URJCMakerGroup/TFG-Cristina-Fernandez/Images/Big/Esquema_funcionamiento_mesa_modelado.png

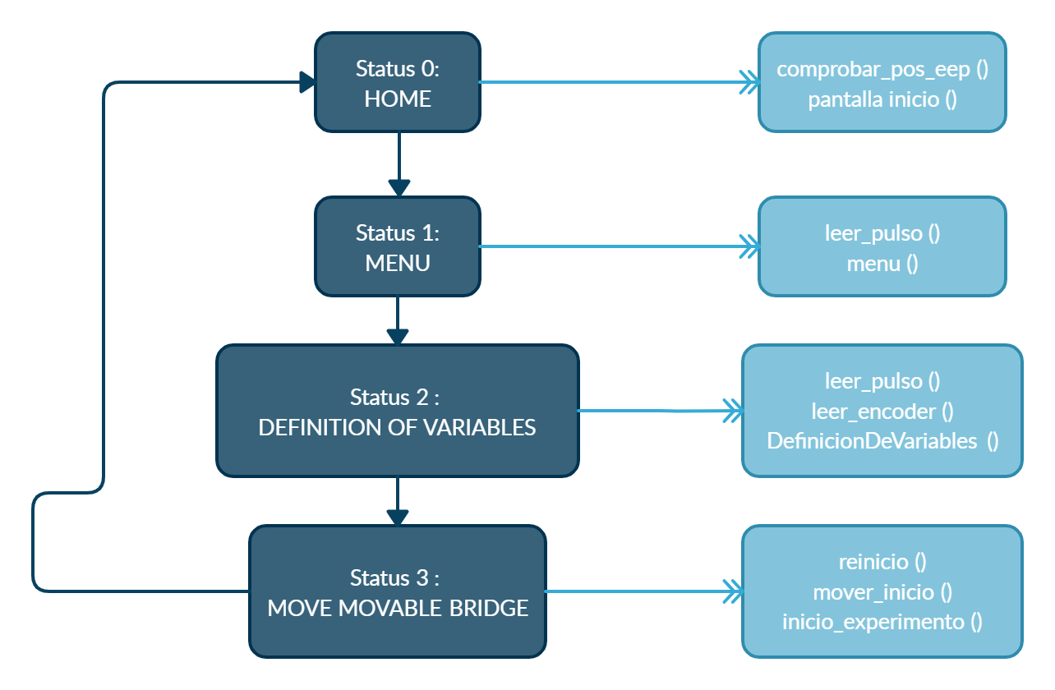
Images/Big/Esquema_funcionamiento_mesa_modelado.png
