URJCMakerGroup/TFG-Cristina-Fernandez/Images/Big/EtapaB.PNG

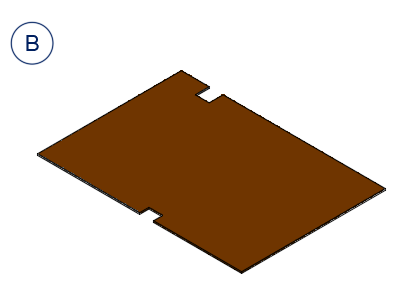
Images/Big/EtapaB.PNG
