URJCMakerGroup/TFG-Cristina-Fernandez/Images/Big/EtapaC.PNG

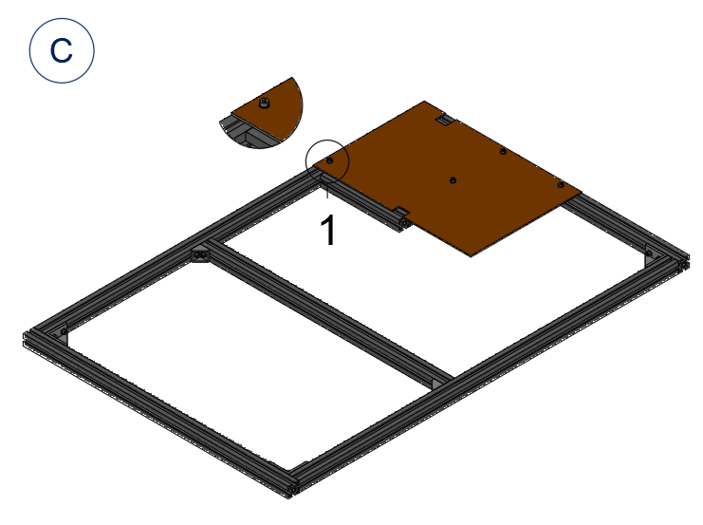
Images/Big/EtapaC.PNG
