URJCMakerGroup/TFG-Cristina-Fernandez/Images/Big/EtapaD.PNG

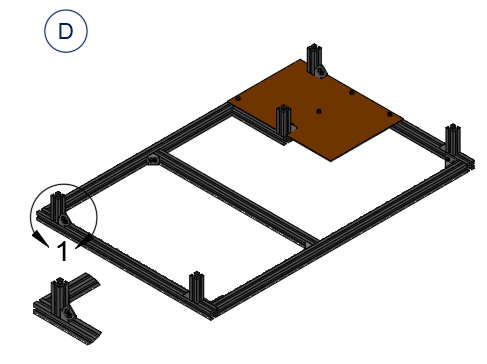
Images/Big/EtapaD.PNG
