URJCMakerGroup/TFG-Cristina-Fernandez/Images/Big/EtapaE.PNG

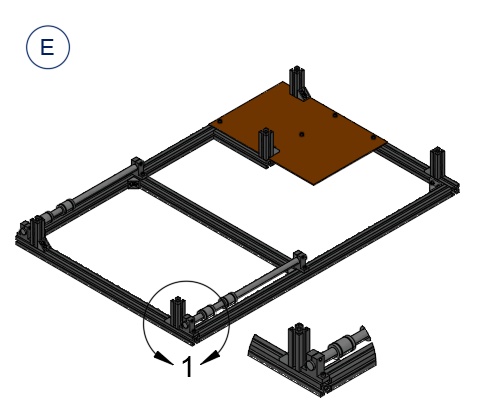
Images/Big/EtapaE.PNG
