URJCMakerGroup/TFG-Cristina-Fernandez/Images/Big/EtapaF.PNG

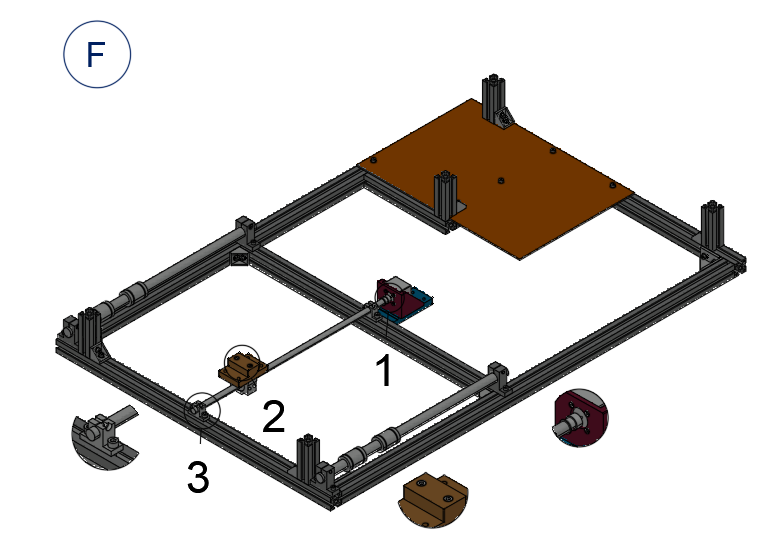
Images/Big/EtapaF.PNG
