URJCMakerGroup/TFG-Cristina-Fernandez/Images/Big/EtapaG.PNG

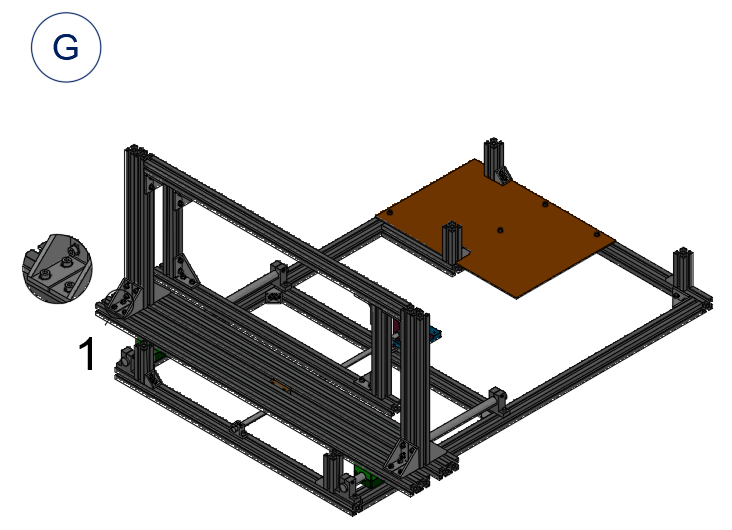
Images/Big/EtapaG.PNG
