URJCMakerGroup/TFG-Cristina-Fernandez/Images/Big/EtapaH.PNG

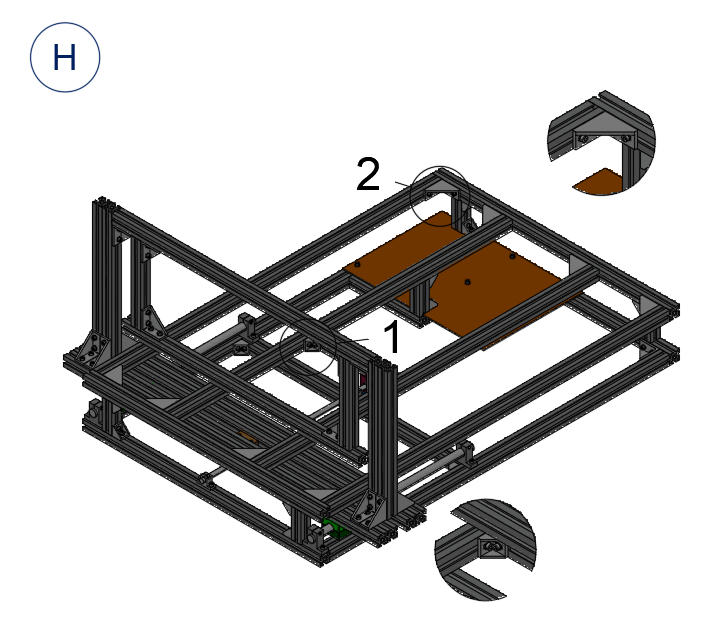
Images/Big/EtapaH.PNG
