URJCMakerGroup/TFG-Cristina-Fernandez/Images/Big/EtapaI.PNG

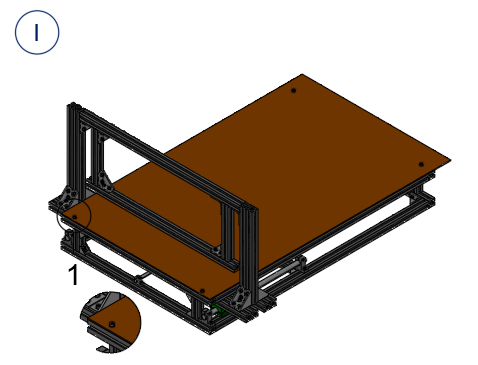
Images/Big/EtapaI.PNG
