URJCMakerGroup/TFG-Cristina-Fernandez/Images/Big/Mesa_modelado.png

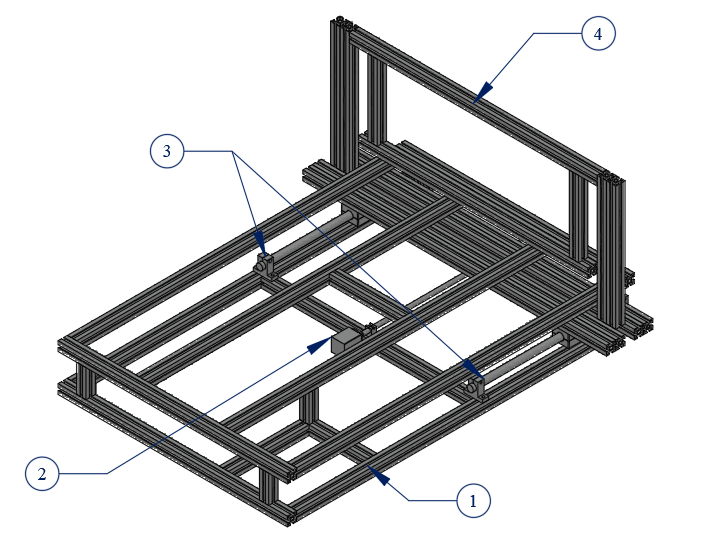
Images/Big/Mesa_modelado.png
