URJCMakerGroup/TFG-Cristina-Fernandez/Images/Big/OSHW_mark_ES000021.png

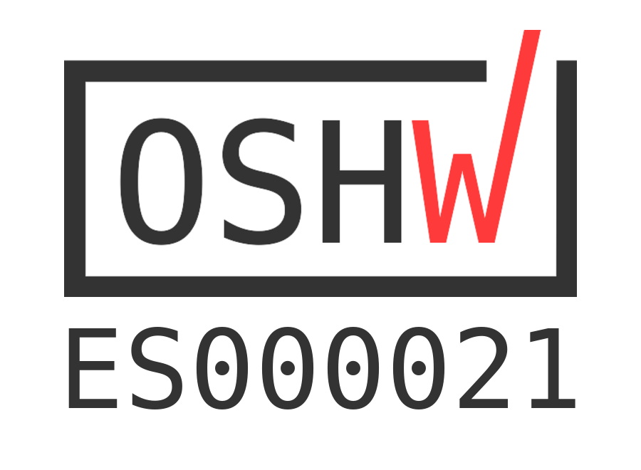
Images/Big/OSHW_mark_ES000021.png
