URJCMakerGroup/TFG-Cristina-Fernandez/Images/Big/Pantalla_LCD.PNG

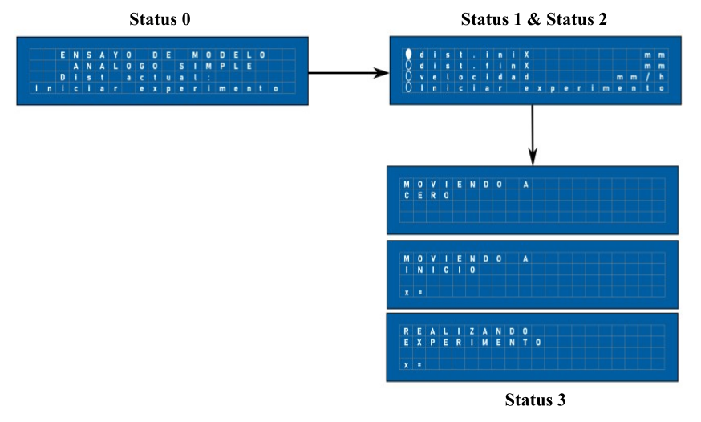
Images/Big/Pantalla_LCD.PNG
