URJCMakerGroup/TFG-Cristina-Fernandez/Images/Big/Simulador.PNG

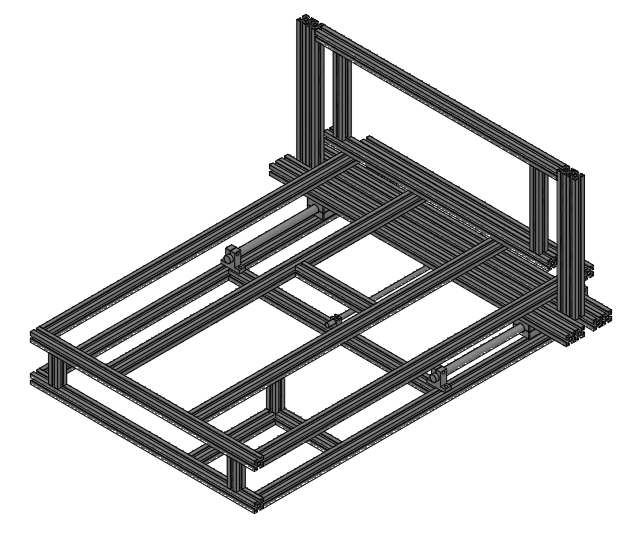
Images/Big/Simulador.PNG
