URJCMakerGroup/TFG-Cristina-Fernandez/Images/Big/Simulador_tablas.PNG

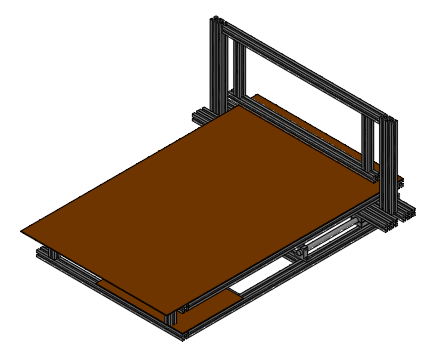
Images/Big/Simulador_tablas.PNG
