URJCMakerGroup/TFG-Cristina-Fernandez/img/Big/Soporte_Cojinete_superior.PNG

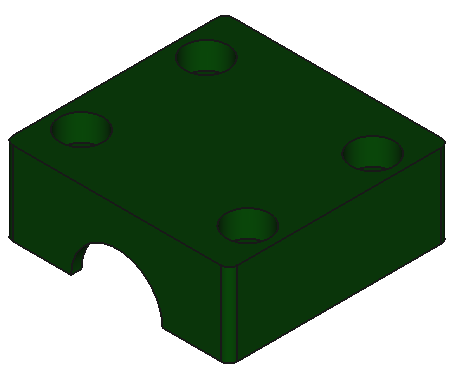
img/Big/Soporte_Cojinete_superior.PNG
