URJCMakerGroup/TFG-Cristina-Fernandez/src/geo_mesa.py

# ----------------------------------------------------------------------------
# -- Simulador geologico
# ----------------------------------------------------------------------------
# -- (c) Felipe Machado
# -- Area of Electronic Technology. Rey Juan Carlos University (urjc.es)
# -- July-2019
# ----------------------------------------------------------------------------
# --- LGPL Licence
# ----------------------------------------------------------------------------

# to execute from the FreeCAD console:
#  execute freecad from the cmd console on the directory
# "C:\Program Files\FreeCAD 0.16\bin\freecad" base.py

# to excute from command line in windows:
# "C:\Program Files\FreeCAD 0.16\bin\freecadcmd" base.py

# with FreeCAD 0.18 Python 3
#exec(open("geo_mesa.py").read())

import os
import sys
import math
import FreeCAD
import FreeCADGui
import Part
import Draft
import logging  # to avoid using print statements
import time
#import copy
#import Mesh
import DraftVecUtils


# to get the current directory. Freecad has to be executed from the same
# directory this file is
filepath = os.getcwd()
#filepath = "./"
#filepath = "F/urjc/proyectos/2016_platform_cell/device/planos/python/"
#filepath = "C:/Users/felipe/urjc/proyectos/2016_platform_cell/device/planos/python/"


# to get the components
# In FreeCAD can be added: Preferences->General->Macro->Macro path
sys.path.append(filepath) 
# Either one of these 2 to select the path, inside the tree, copied by
# git subtree, or in its one place
#sys.path.append(filepath + '/' + 'modules/comps')
sys.path.append(filepath + '/' + '../../comps')

import fcfun   # import my functions for freecad. FreeCad Functions
import kcomp   # import material constants and other constants
import comps   # import my CAD components
import parts   # import my CAD components to print

from fcfun import V0, VX, VY, VZ, V0ROT, addBox, addCyl, fillet_len
from fcfun import VXN, VYN, VZN
from fcfun import addBolt, addBoltNut_hole, NutHole
from kcomp import TOL

def str_neg (num, p=0, n=0):
    """ Just a function to have the names of componentes when using for
    to differenciate them if the index is negative. FreeCAD name cannot
    have negative, so writting a 'n' instead of a '-'
    
    Parameters:
    ----------
    num : int
        the number (index of a for loop)
    p : int
        0: doesnt write a p when number is positive
        1: writes a p when number is positive
    n : int
        0: doesnt write the number, just the n or p (if p=1)
        1: writes the number, and the n if the case (or p)
    """

    if num < 0:
       if n == 0: # dont write the number
           return 'n'
       else: # write the number
           return 'n' + str(abs(num))
    else: # positive
       if n == 0: # dont write the number
           if p == 0:
               return ''
           else: # write the p, not the number
               return 'p'
       else: # write the number
           if p == 0:
               return str(num)
           else: # write the p and the number
               return 'p' + str(num)



# Taking the same axis as the 3D printer:
#
#    Z   Y
#    | /               USING THIS ONE
#    |/___ X
# 
# centered on the cubes and the vertical line of the camera and the objective
#
# as seen from the front
# be careful because at the beginning I was considering:
#      Z
#      |
#      |___ Y       NOT USING THIS ONE
#     /
#    / X
#
# In this design, the bas will be centered on X

logging.basicConfig(level=logging.DEBUG,
                    format='%(asctime)s - %(levelname)s - %(message)s')

doc = FreeCAD.newDocument()

#Gui.ActiveDocument = Gui.getDocument(doc.Label)
#guidoc = Gui.getDocument(doc.Label)


# file to save the components and their dimensions. Kind of a BOM,
# bill of materials
file_comps = open ('geo_bom.txt', 'w')

tot_d = 1000 #largo (profundidad interna)
tot_w = 740 #ancho
alu_w = 30 # ancho de los perfiles

alu_len_d = tot_d + 2 * alu_w  #perfiles a lo largo (profundo)
alu_len_v = 90  #perfiles a lo alto para mesa REVISAR
alu_len_w = tot_w #perfiles a lo ancho
alu_len_w_int1 = tot_w - 2 * alu_w #perfil a lo ancho interior de la base de la estructura
alu_len_w_int2 = tot_w #perfiles a lo ancho interiores del puente móvil

# portico horizontal parte arriba
alu_len_gantry = tot_w + 60. # poner un extra para que no rocen (mirar)

# carriage width (length=
#2: each side. 3: to have a double profile and a double bracket
alu_car_l = tot_w + 2 * 3 * alu_w + 60. #(mirar)

carro_color = fcfun.ORANGE_08
empuje_color = fcfun.GREEN_07
w_color = fcfun.BLUE_07

d_alu = kcomp.ALU_PROF[alu_w]

# zero in the Y of motor leadscrew support, centered on Y
# Z on top of the aluminum profiles
pos_0_x = 0.
pos_0_y = 0.
pos_0_z = 0.

# todas las posiciones como si pos_0 estuviese en (0,0,0)
pos_0 = FreeCAD.Vector(pos_0_x, pos_0_y, pos_0_z)

rod_d = 20. #diameter of the rods

leadscrew_tot_l = 510. #(mirar)
leadscrew_motor_space_l = 30.
leadscrew_int_l = leadscrew_tot_l - leadscrew_motor_space_l
leadscrew_d = 12 # trapecial, or 16.

# perfiles del portico en altura
alu_len_port_v = 400

# perfiles que bajan del portico para empujar
alu_len_empuje_v = 244

alu_tray_name = 'alu_tray'

# travesano interno para el final del husillo y su soporte
alu_base_traves_int_pos = DraftVecUtils.scale(VY, leadscrew_int_l-alu_w/2)
h_alu = comps.getaluprof_dir(d_alu, length=alu_len_w_int1,
                                 fc_axis_l = VX,
                                 fc_axis_w = VY,
                                 fc_axis_p = VZN,
                                 ref_l = 1, # centered
                                 ref_w = 1, # centered
                                 ref_p = 2, # at top
                                 wfco = 1,
                                 pos = alu_base_traves_int_pos + pos_0,
                                 name = 'travesano_int')

print ('travesanos ancho: ', str(alu_len_w))
# los travesanos en direccion x, cubren el ancho
for y_i in [0,1]:  # 
    alu_name = 'alu_travesano_base' + '_y' + str(y_i)
    alu_base_traves_pos = DraftVecUtils.scale(VY, y_i*(alu_len_d+alu_w))
    h_alu = comps.getaluprof_dir(d_alu, length=alu_len_w,
                                 fc_axis_l = VX,
                                 fc_axis_w = VY,
                                 fc_axis_p = VZN,
                                 ref_l = 1, # centered
                                 ref_w = 1, # centered
                                 ref_p = 2, # at top
                                 wfco = 1,
                                 pos = alu_base_traves_pos + pos_0,
                                 name = alu_name)

# soportes de ejes
for x_i in [-1,1]:  # izquierda y derecha
    sh_pos1 = alu_base_traves_int_pos + DraftVecUtils.scale(VX, x_i*tot_w/2) 
    sh_name1 = 'sh_' + '_y' + str(1) + '_x' + str_neg(x_i)
    h_sh8_1 = comps.Sk_dir(size=rod_d,
                         fc_axis_h = VZ,
                         fc_axis_d = VY,
                         fc_axis_w = DraftVecUtils.scale(VXN,x_i),
                         ref_hr = 0,
                         ref_wc = -1, #at the end
                         ref_dc = 1,
                         tol=0, # not to print
                         pos=sh_pos1 + pos_0,
                         name = sh_name1)
    
    sh_pos2 = DraftVecUtils.scale(VX, x_i*tot_w/2) 
    sh_name2 = 'sh_' + '_y' + str(2) + '_x' + str_neg(x_i)
    h_sh8_2 = comps.Sk_dir(size=rod_d,
                         fc_axis_h = VZ,
                         fc_axis_d = VY,
                         fc_axis_w = DraftVecUtils.scale(VXN,x_i),
                         ref_hr = 0,
                         ref_wc = -1, #at the end
                         ref_dc = 1,
                         tol=0, # not to print
                         pos=sh_pos2 + pos_0,
                         name = sh_name2)
    

file_comps.write('perfiles de la base y mesa 30x30, travesanos: \n')
file_comps.write('4 x ' + str(alu_len_w) + ' \n')
file_comps.write('      perfil interno soporte husillo (alguno mas) \n')
file_comps.write('4 x ' + str(alu_len_w_int1) + ' \n')

# height of the axis, from pos_0
axis_h = h_sh8_1.axis_h

# distance from the side to the center of the SH
axis_cen_w = h_sh8_1.tot_w/2

axis_len = alu_len_d/2. - alu_w


#dictionary of the linear bearing housing
d_linbear_house = kcomp.SCE20UU_Pr30b

# separacion de los postes verticales del portico de la mesa, a cada lado
port_sep = 30.

print ('largeros: largo: ', str(alu_len_d))
# los largueros en direccion y, cubren la profundidad (depth)
for x_i in [-1,1]:  # izquierda y derecha
    alu_name = 'alu_largo_base' + '_x' + str_neg(x_i)
    alu_base_largo_pos = (DraftVecUtils.scale(VX, x_i*tot_w/2) 
                             + DraftVecUtils.scale(VY, alu_w/2) )

    h_alu = comps.getaluprof_dir(d_alu, length=alu_len_d,
                                 fc_axis_l = VY,
                                 fc_axis_w = DraftVecUtils.scale(VXN,x_i),
                                 fc_axis_p = VZN,
                                 ref_l = 2, # from the side
                                 ref_w = 2, # from the side
                                 ref_p = 2, # at top
                                 wfco = 1,
                                 pos = alu_base_largo_pos + pos_0,
                                 name = alu_name)

    # ejes
    axis_pos = (DraftVecUtils.scale(VX, x_i*(tot_w/2-axis_cen_w)) 
                      + DraftVecUtils.scale(VY, -alu_w/2)
                      + DraftVecUtils.scale(VZ, axis_h)  )
    
    shp_rod = fcfun.shp_cyl_gen(r = rod_d/2., h=axis_len,
                              axis_h = VY,
                              pos_h = 1,
                              pos = axis_pos + pos_0)
    Part.show(shp_rod)

    for y_i in [0,1]:  # 
        # Para uno de 4, todos en una pieza
        linbear_pos_y = DraftVecUtils.scale(VY,3*alu_w + y_i*alu_w)
        linbear1_pos_y = DraftVecUtils.scale(VY,3*alu_w)
        linbear_pos_y = DraftVecUtils.scale(VY,3*alu_w + y_i*3*alu_w)
        linbear_pos  = axis_pos + linbear_pos_y
        h_linbear_house = parts.LinBearHouse(d_linbear_house,
                                             fc_slide_axis = VY,
                                             fc_bot_axis=VZ,
                                             axis_center = 1,
                                             mid_center = 1,
                                             pos = linbear_pos + pos_0)
        # height of the base of the aluminum profile of carriage, from pos_0

        alu_carr_trav_h = kcomp.SCE20UU_Pr30b['axis_h']

        # perfiles del carro
        if x_i == 1: # estan centrados en x
            alu_car_name = 'alu_car'
            for it_y in [-1,0]: # a double profile
                alu_car_pos  = (DraftVecUtils.scale(VZ, axis_h)
                + DraftVecUtils.scale(VZ, alu_carr_trav_h)
                + linbear_pos_y +
                + DraftVecUtils.scale(VY,it_y*d_linbear_house['bolt_sep_l']))
               
                h_alu = comps.getaluprof_dir(d_alu, length=alu_car_l,
                                             fc_axis_l = VX,
                                             fc_axis_w = VY,
                                             fc_axis_p = VZ,
                                             ref_l = 1, # centered
                                             ref_w = 1, # centered
                                             ref_p = 2, # at bottom
                                             wfco = 1,
                                             pos = alu_car_pos + pos_0,
                                             name = alu_car_name)
                #h_alu.color(carro_color)

    #perfiles verticales del portico, no se si dobles a simples
    # solo hay uno por cada lado
    port_pos_y = linbear1_pos_y + DraftVecUtils.scale(VY, alu_w)
    port_pos_z = DraftVecUtils.scale(VZ, axis_h + alu_carr_trav_h + alu_w)
    for it_x in[0,1]: # a double profile
        alu_port_name = 'alu_port_v' + str_neg(x_i,p=1, n=0)
        alu_port_v_pos  = (port_pos_y + port_pos_z
           + DraftVecUtils.scale(VX,x_i*(port_sep + alu_len_w/2. +it_x*alu_w)))
               
        h_alu = comps.getaluprof_dir(d_alu, length=alu_len_port_v,
                                      fc_axis_l = VZ,
                                      fc_axis_w = DraftVecUtils.scale(VX,x_i),
                                      fc_axis_p = VY,
                                      ref_l = 2, # at bottom
                                      ref_w = 2, # at the end
                                      ref_p = 1, # centered
                                      wfco = 1,
                                      pos = alu_port_v_pos + pos_0,
                                      name = alu_port_name)
        #h_alu.color(carro_color)

topgantry_pos_z = port_pos_z + DraftVecUtils.scale(VZ, alu_len_port_v)
topgantry_pos = port_pos_y + topgantry_pos_z
h_alu_topgantry = comps.getaluprof_dir(d_alu, length=alu_len_gantry,
                                      fc_axis_l = VX,
                                      fc_axis_w = VY,
                                      fc_axis_p = VZN,
                                      ref_l = 1, # centered bottom
                                      ref_w = 1, # centered
                                      ref_p = 2, # at top
                                      wfco = 1,
                                      pos = topgantry_pos + pos_0,
                                      name = 'top_gantry')

#h_alu_topgantry.color(carro_color)

empuje_v_pos_z = topgantry_pos_z + DraftVecUtils.scale(VZN, alu_w)

# perfiles que bajan del portico para empujar
for x_i in [-1,1]:  # izquierda y derecha
    alu_name = 'alu_empuje_v' + '_x' + str_neg(x_i, p=1)
    empuje_v_pos_x = DraftVecUtils.scale(VX, x_i * (alu_len_w_int2/2. - 30.))
    empuje_v_pos = empuje_v_pos_x + port_pos_y + empuje_v_pos_z 
    h_alu_empuje_v = comps.getaluprof_dir(d_alu, length=alu_len_empuje_v,
                                      fc_axis_l = VZN,
                                      fc_axis_w = DraftVecUtils.scale(VXN,x_i),
                                      fc_axis_p = VY,
                                      ref_l = 2, # from top
                                      ref_w = 2, # from outer side
                                      ref_p = 1, # centered
                                      wfco = 1,
                                      pos = empuje_v_pos + pos_0,
                                      name = alu_port_name)
    #h_alu_empuje_v.color(empuje_color)

file_comps.write('perfiles que bajan del portico para empujar\n')
file_comps.write('4 x ' + str(alu_len_empuje_v) + '\n')

file_comps.write('perfiles que bajan del portico para empujar (otra altura)\n')
file_comps.write('4 x ' + str(alu_len_empuje_v-50) + '\n')

file_comps.write('\n2 Ejes: \n')
file_comps.write('largo:' + str(axis_len) + '  diametro :' + str(rod_d) + '\n\n')

# perfil de la base del empuje
base_empuje_pos_z = empuje_v_pos_z + DraftVecUtils.scale(VZN, alu_len_empuje_v)
base_empuje_pos = port_pos_y + base_empuje_pos_z 
h_alu_base_empuje = comps.getaluprof_dir(d_alu, length=alu_len_w_int2,
                                      fc_axis_l = VX,
                                      fc_axis_w = VY,
                                      fc_axis_p = VZN,
                                      ref_l = 1, # from top
                                      ref_w = 1, # from outer side
                                      ref_p = 2, # from top
                                      wfco = 1,
                                      pos = base_empuje_pos + pos_0,
                                      name = 'alu_base_empuje')
#h_alu_base_empuje.color(empuje_color)

file_comps.write('largueros de la base y mesa, dos más a lo largo \n')
file_comps.write('6 x ' + str(alu_len_d) + '\n')
file_comps.write('perfiles del carro 2x30x30 (dobles) \n')
file_comps.write('2 x ' + str(alu_car_l) + '\n')

file_comps.write('perfil de la base del empuje\n')
file_comps.write( str(alu_len_w_int2) + '\n')

file_comps.write('perfil de la base del empuje: extras (-60)\n')
file_comps.write( str(alu_len_w_int2-60) + '\n')

file_comps.write('perfil de la base del empuje: extras (-120)\n')
file_comps.write( str(alu_len_w_int2-120) + '\n')

min_mesa_h = axis_h + alu_carr_trav_h + alu_w
print('altura entre perfil de la base (top) y perfil del carro (top): ')
print(str(min_mesa_h), '\n')
            
# para tenerlo en la siguiente decena más alta, y con minimo 2 mm
mesa_h = 10* math.ceil((min_mesa_h +2) / 10.)
if (mesa_h - min_mesa_h) > 15:
    mesa_h = mesa_h - 10
print (str(mesa_h))

file_comps.write('perfiles del portico 2x30x30 (dobles) \n')
file_comps.write('2 x ' + str(alu_len_port_v) + '\n')
file_comps.write('también pueden ser simples 30x30 \n')
file_comps.write('2 x ' + str(alu_len_port_v) + '\n')
file_comps.write('puente del portico \n')
file_comps.write('1 x ' + str(alu_len_gantry) + '\n')

file_comps.write('altura entre perfil de la base (top) y perfil de carro (top): ')
file_comps.write(str(min_mesa_h) + '\n')

file_comps.write('perfiles elevacion mesa 30x30 \n')
file_comps.write('10 x ' + str(mesa_h) + '\n')

for x_i in [-1,1]:  # izquierda y derecha
   for y_i in [0,1]:  #delante y detras
       pos_alu_v = (pos_0 + DraftVecUtils.scale(VY, y_i*(alu_len_d+alu_w))
                         + DraftVecUtils.scale(VX, x_i*(tot_w/2-2*axis_cen_w))) 
       h_alu_v = comps.getaluprof_dir(d_alu, length=mesa_h,
                                   fc_axis_l = VZ,
                                   fc_axis_w = DraftVecUtils.scale(VXN,x_i),
                                   fc_axis_p = VY,
                                   ref_l = 2, # at bottom
                                   ref_w = 2, # at the end
                                   ref_p = 1, # centered
                                   wfco = 1,
                                   pos = pos_alu_v,
                                   name = 'alu_v')

#Perfiles de la mesa, ya contabilizados arriba, porque son las mismas
# dimensiones que la base
for y_i in [0,1]:  # 
    alu_name = 'alu_travesano_mesa' + '_y' + str(y_i)
    alu_base_traves_pos = (pos_0
                           + DraftVecUtils.scale(VY, y_i*(alu_len_d+alu_w))
                           + DraftVecUtils.scale(VZ,mesa_h))
    h_alu = comps.getaluprof_dir(d_alu, length=alu_len_w,
                                 fc_axis_l = VX,
                                 fc_axis_w = VY,
                                 fc_axis_p = VZ,
                                 ref_l = 1, # centered
                                 ref_w = 1, # centered
                                 ref_p = 2, # at top
                                 wfco = 1,
                                 pos = alu_base_traves_pos,
                                 name = alu_name)

for x_i in [-1,1]:  # izquierda y derecha
    alu_name = 'alu_largo_mesa' + '_x' + str_neg(x_i)
    alu_mesa_largo_pos = (pos_0 + DraftVecUtils.scale(VX, x_i*tot_w/2) 
                             + DraftVecUtils.scale(VY, alu_w/2) 
                           + DraftVecUtils.scale(VZ,mesa_h))

    h_alu = comps.getaluprof_dir(d_alu, length=alu_len_d,
                                 fc_axis_l = VY,
                                 fc_axis_w = DraftVecUtils.scale(VXN,x_i),
                                 fc_axis_p = VZ,
                                 ref_l = 2, # from the side
                                 ref_w = 2, # from the side
                                 ref_p = 2, # at top
                                 wfco = 1,
                                 pos = alu_mesa_largo_pos,
                                 name = alu_name)

# Pillow block soporte de husillo (dibujo aproximado)
for y_i in [0,1]:  # delante detras
    pillow_pos = DraftVecUtils.scale(VY, y_i*(leadscrew_int_l-alu_w/2)) 
    pillow_name = 'pillow_' + '_y' + str(y_i) 
    h_pillow = comps.Sk_dir(size=leadscrew_d,
                             fc_axis_h = VZ,
                             fc_axis_d = VY,
                             fc_axis_w = VX,
                             ref_hr = 0,
                             ref_wc = 1, #centered
                             ref_dc = 1,
                             pillow = 1,
                             tol=0, # not to print
                             pos= pillow_pos + pos_0,
                             name = pillow_name)

# tornillo sin fin
leads_pos = ( DraftVecUtils.scale(VZ, h_pillow.axis_h)
            + DraftVecUtils.scale(VYN, alu_w/2))
shp_leads = fcfun.shp_cyl_gen(r = leadscrew_d/2., h=leadscrew_tot_l,
                              axis_h = VY,
                              pos_h = 1,
                              pos = leads_pos + pos_0)
Part.show(shp_leads)

motor_pos = leads_pos + DraftVecUtils.scale(VY,leadscrew_tot_l)
nema_motor = comps.PartNemaMotor (
                              nema_size = 17,
                              base_l = 56.,
                              shaft_l = 21.,
                              shaft_r = 6.35/2.,
                              circle_r = 47.14/2.,
                              circle_h = 1.6,
                              #chmf_r = chmf_r, 
                              rear_shaft_l= 0,
                              bolt_depth = 5.,
                              #bolt_out  = 0,
                              #cut_extra = 0,
                              axis_d = VZ,
                              axis_w = VX,
                              axis_h = VYN,
                              pos_d = 0,
                              pos_w = 0,
                              pos_h = 2,
                              pos = motor_pos + pos_0)

# los largueros en direccion que sirven de soporte para la tabla
alu_largo_sop = 240
sep_alu_largo = alu_largo_sop + 2 * alu_w

for x_i in [-1,1]:  # izquierda y derecha
    alu_name = 'alu_largo' + '_x' + str_neg(x_i)
    alu_largo_pos = (DraftVecUtils.scale(VX, x_i * sep_alu_largo/2) 
                             + DraftVecUtils.scale(VY, alu_w/2) 
                             + DraftVecUtils.scale(VZ, alu_len_v + alu_w))

    h_alu = comps.getaluprof_dir(d_alu, length=alu_len_d,
                                 fc_axis_l = VY,
                                 fc_axis_w = DraftVecUtils.scale(VXN,x_i),
                                 fc_axis_p = VZN,
                                 ref_l = 2, # from the side
                                 ref_w = 2, # from the side
                                 ref_p = 2, # at top
                                 wfco = 1,
                                 pos = alu_largo_pos + pos_0,
                                 name = alu_name)

# travesano interno superior para el soporte de la tabla
alu_traves_int_sup_pos = (DraftVecUtils.scale(VY, leadscrew_int_l-alu_w/2)
                                 + DraftVecUtils.scale(VZ, alu_len_v + alu_w))

h_alu = comps.getaluprof_dir(d_alu, length=alu_largo_sop,
                                 fc_axis_l = VX,
                                 fc_axis_w = VY,
                                 fc_axis_p = VZN,
                                 ref_l = 1, # centered
                                 ref_w = 1, # centered
                                 ref_p = 2, # at top
                                 wfco = 1,
                                 pos = alu_traves_int_sup_pos + pos_0,
                                 name = 'travesano_int_sup')

# el travesano en direccion x que soporta la tabla con la fuente de alimentación y el Arduino
alu_largo_sop_x = 220
alu_largo_sop_y = 260
alu_traves_sop_x_pos = (DraftVecUtils.scale(VX, (-1)*tot_w/2 + alu_largo_sop_x/2 + alu_w) 
                         + DraftVecUtils.scale(VY, alu_len_d - alu_largo_sop_y))
h_alu = comps.getaluprof_dir(d_alu, length=alu_largo_sop_x,
                             fc_axis_l = VX,
                             fc_axis_w = VY,
                             fc_axis_p = VZN,
                             ref_l = 1, # centered
                             ref_w = 1, # centered
                             ref_p = 2, # at top
                             wfco = 1,
                             pos = alu_traves_sop_x_pos + pos_0,
                             name = 'alu_travesano_sop_x')    

# el travesano en direccion y que soporta la tabla con la fuente de alimentación y el Arduino 
alu_traves_sop_y_pos = (DraftVecUtils.scale(VX, (-1)*tot_w/2 + alu_largo_sop_x + alu_w/2) 
                         + DraftVecUtils.scale(VY, alu_len_d + alu_w/2 - alu_largo_sop_y/2))

h_alu = comps.getaluprof_dir(d_alu, length=alu_largo_sop_y,
                             fc_axis_l = VY,
                             fc_axis_w = VX,
                             fc_axis_p = VZN,
                             ref_l = 1, # centered
                             ref_w = 1, # centered
                             ref_p = 2, # at top
                             wfco = 1,
                             pos = alu_traves_sop_y_pos + pos_0,
                             name = 'alu_travesano_sop_y')    

# el travesano en direccion z 
alu_traves_sop_z_pos = (DraftVecUtils.scale(VX, (-1)*tot_w/2 + alu_largo_sop_x + alu_w) 
                         + DraftVecUtils.scale(VY, alu_len_d - alu_largo_sop_y))

h_alu = comps.getaluprof_dir(d_alu, length=mesa_h,
                             fc_axis_l = VZ,
                             fc_axis_w = VXN,
                             fc_axis_p = VY,
                             ref_l = 2, # centered
                             ref_w = 2, # centered
                             ref_p = 1, # at top
                             wfco = 1,
                             pos = alu_traves_sop_z_pos + pos_0,
                             name = 'alu_travesano_sop_z')                       

file_comps.close()
doc.recompute()
